labic-ifs/promaker/imagens/Robô Montado.jpeg

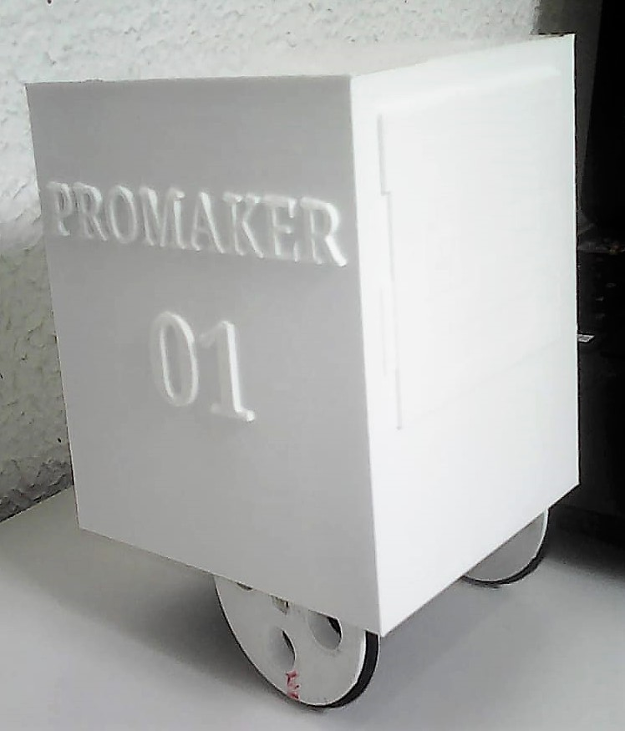
imagens/Robô Montado.jpeg
